NextGen-Environmental-Sensor-Lab/Mouse-City/Images/City Mouse Cages 1.jpg

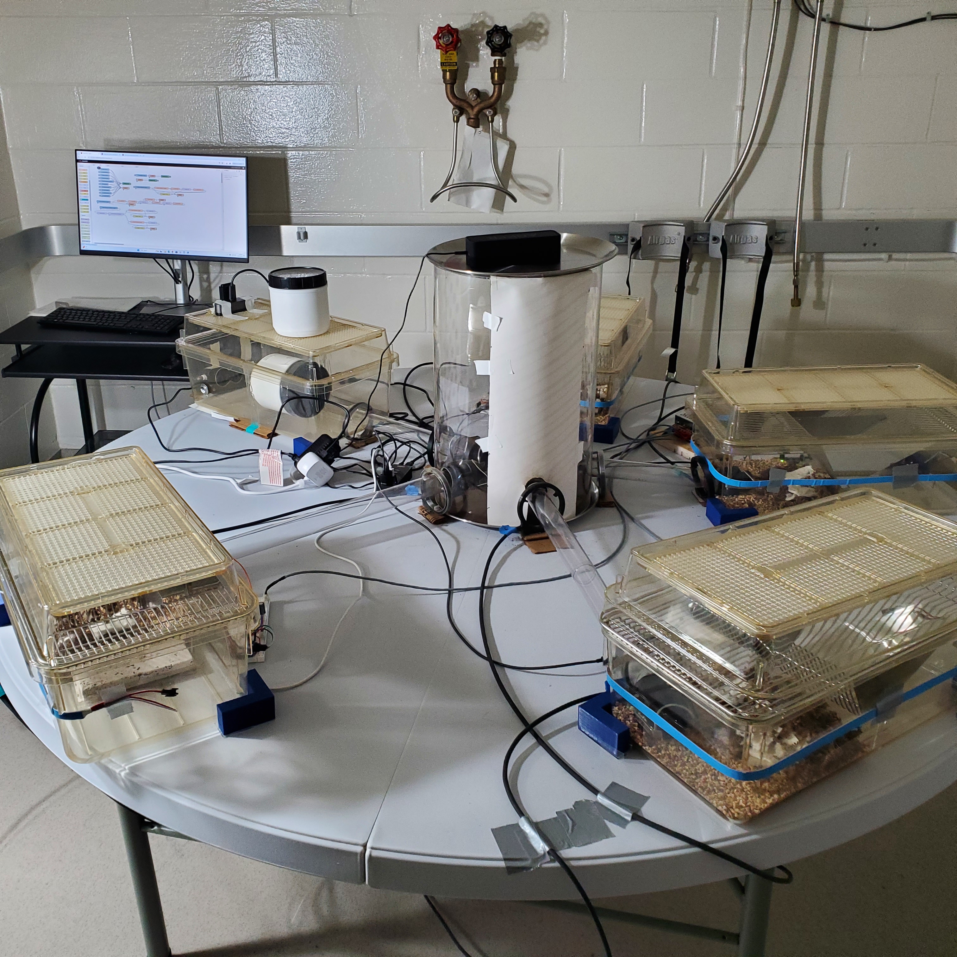
Images/City Mouse Cages 1.jpg
