NextGen-Environmental-Sensor-Lab/Mouse-City/Images/City Mouse Cages 2.jpg

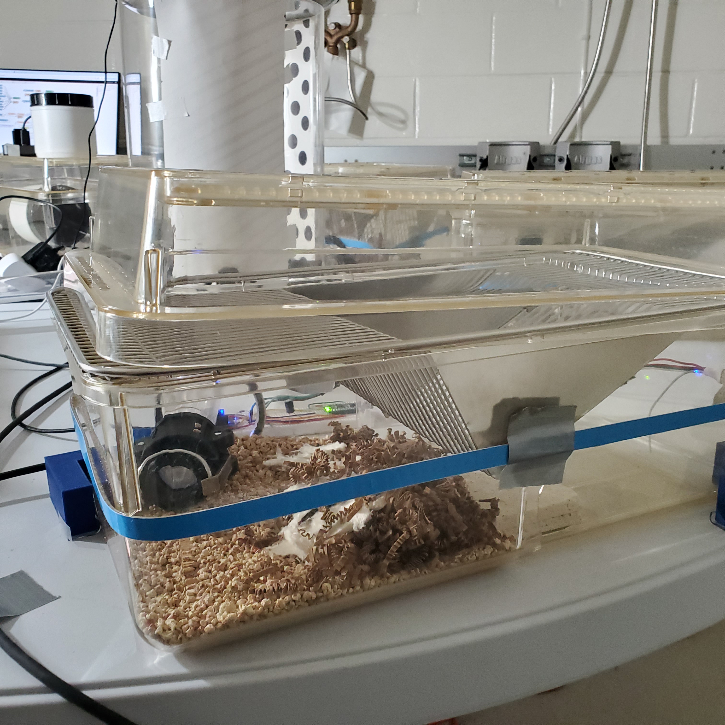
Images/City Mouse Cages 2.jpg
