NextGen-Environmental-Sensor-Lab/Mouse-City/Images/Mouse City Block Diagram.PNG

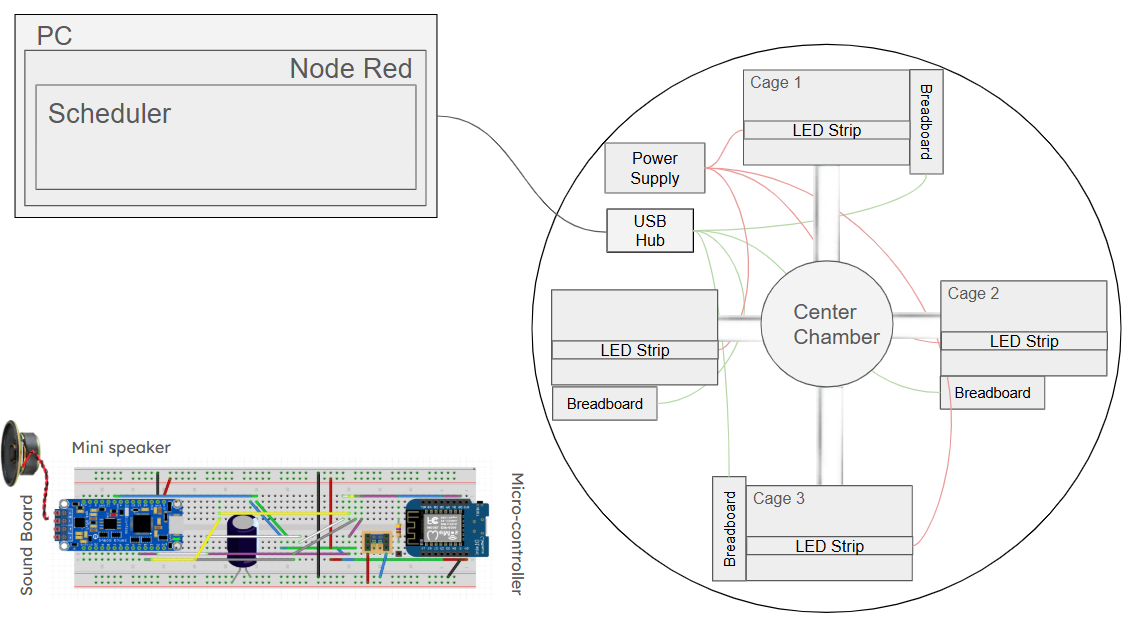
Images/Mouse City Block Diagram.PNG
