NextGen-Environmental-Sensor-Lab/Mouse-City/Images/Mouse City Fritzing.PNG

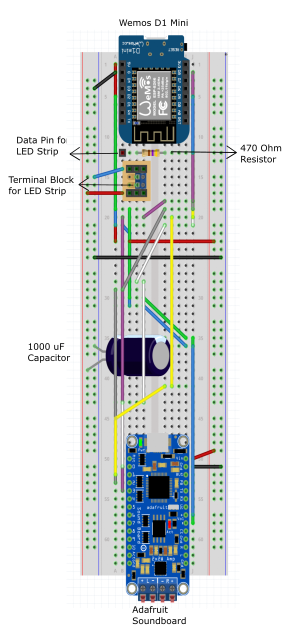
Images/Mouse City Fritzing.PNG
